jack-d-long/lorawan-map/tracker-hardware/firmware/feather_sd_sam-m8q/Catena_Fram32k.h

/* Catena_Fram2k.h	Sun Mar 12 2017 17:47:52 tmm */

/*

Module:  Catena_Fram2k.h

Function:
	class McciCatena::cFram2k

Version:
	V0.5.0	Sun Mar 12 2017 17:47:52 tmm	Edit level 1

Copyright notice:
	This file copyright (C) 2017 by

		MCCI Corporation
		3520 Krums Corners Road
		Ithaca, NY  14850

	An unpublished work.  All rights reserved.

	This file is proprietary information, and may not be disclosed or
	copied without the prior permission of MCCI Corporation.

Author:
	Terry Moore, MCCI Corporation	March 2017

Revision history:
   0.5.0  Sun Mar 12 2017 17:47:52  tmm
	Module created.

*/

#ifndef _CATENA_FRAM32K_H_		/* prevent multiple includes */
#define _CATENA_FRAM32K_H_

#pragma once

#ifndef _CATENA_FRAM_H_
# include "Catena_Fram.h"
#endif

#ifndef _MCCI_FRAM_I2C_H_
//# include <MCCI_FRAM_I2C.h>
#include "Ece4950_Mcci_Fram.h"
#endif

/****************************************************************************\
|
|	The contents
|
\****************************************************************************/


namespace McciCatena {


class cFram32k : public cFram
	{
protected:
	using Super = cFram;

public:
	cFram32k() { this->m_fReady = false; };
	virtual ~cFram32k() {};

        // begin working with the FRAM
	virtual bool begin() override;

        // read from the store
        virtual size_t read(
                cFramStorage::Offset uOffset, uint8_t *pBuffer, size_t nBuffer
                ) override;

        // write to the store
        virtual bool write(
                cFramStorage::Offset uOffset, const uint8_t *pBuffer, size_t nBuffer
                ) override;

        virtual cFramStorage::Offset getsize() const override
                {
                return 32768;
                };


protected:
private:
	MCCI_FRAM_I2C	m_hw;
	};

}; // namespace McciCatena

/**** end of Catena_Fram2k.h ****/
#endif /* _CATENA_FRAM2K_H_ */
